sensy-one/AirBee/homey/assets/images/airbee-front-large.png

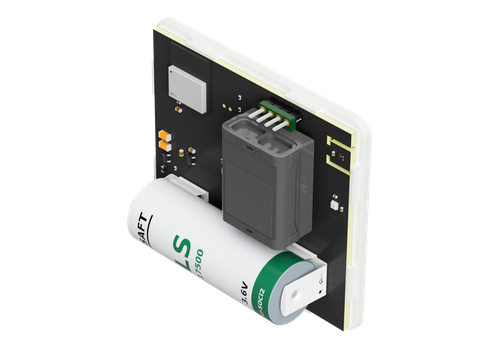
homey/assets/images/airbee-front-large.png
