sensy-one/AirBee/homey/drivers/airbee-ble/assets/images/large.png

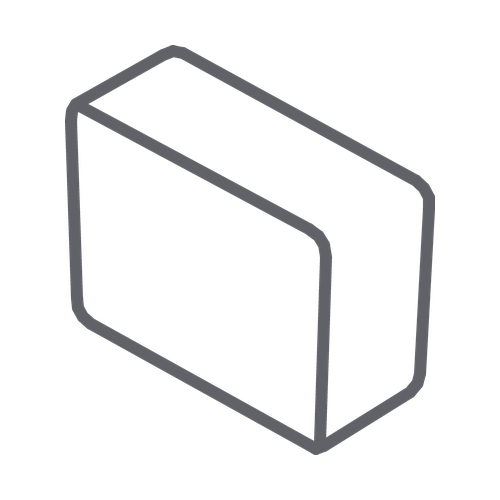
homey/drivers/airbee-ble/assets/images/large.png
